kerpz/ArduinoHondaOBD/images/LCD_01.png

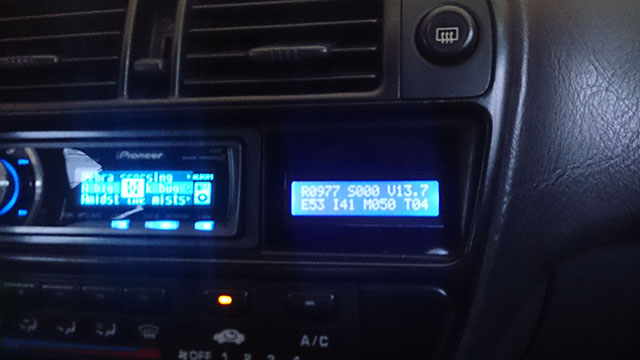
images/LCD_01.png
