kerpz/ArduinoHondaOBD/images/TORQUE_01.png

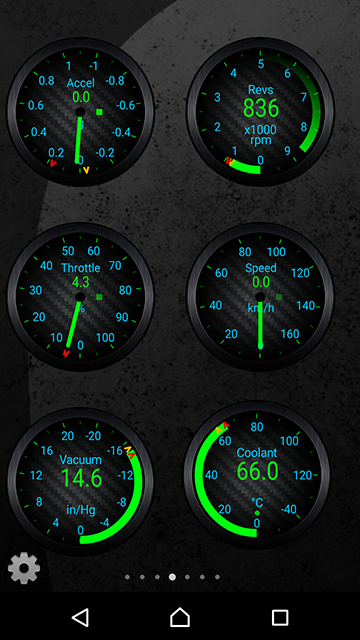
images/TORQUE_01.png
