kerpz/ArduinoHondaOBD/images/TORQUE_02.png

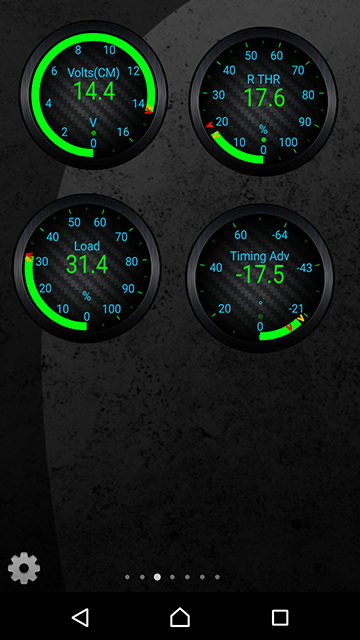
images/TORQUE_02.png
