kerpz/ArduinoHondaOBD/images/TORQUE_04.png

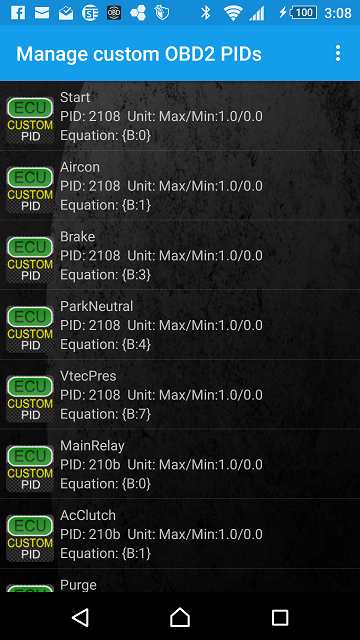
images/TORQUE_04.png
