kerpz/ArduinoHondaOBD/images/LCD_wiring.png

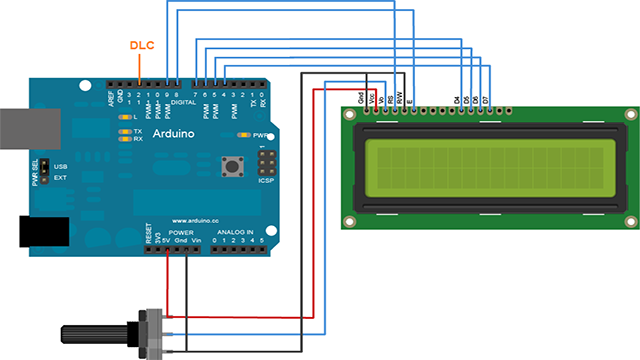
images/LCD_wiring.png
